nf-dj/cellpilot/client/cellpilot.c

/*
 * Copyright (c) 2015 Netforce Co. Ltd.
 * 
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
 * THE SOFTWARE IS PROVIDED "AS IS", WITHOUT WARRANTY OF ANY KIND,
 * EXPRESS OR IMPLIED, INCLUDING BUT NOT LIMITED TO THE WARRANTIES OF
 * MERCHANTABILITY, FITNESS FOR A PARTICULAR PURPOSE AND NONINFRINGEMENT.
 * IN NO EVENT SHALL THE AUTHORS OR COPYRIGHT HOLDERS BE LIABLE FOR ANY CLAIM,
 * DAMAGES OR OTHER LIABILITY, WHETHER IN AN ACTION OF CONTRACT, TORT OR
 * OTHERWISE, ARISING FROM, OUT OF OR IN CONNECTION WITH THE SOFTWARE OR THE USE
 * OR OTHER DEALINGS IN THE SOFTWARE.
 */

#include <SDL2/SDL.h>
#include <SDL2/SDL_ttf.h>
#include <SDL2/SDL2_gfxPrimitives.h>
#include <lua5.1/lua.h>
#include <lua5.1/lauxlib.h>
#include <lua5.1/lualib.h>
#include <stdlib.h>
#include <string.h>
#include "libavcodec/avcodec.h"
#include <libswscale/swscale.h>
#include <math.h>

lua_State *L;

char screen_text[1024];
uint8_t *picture_data;
int picture_w, picture_h;

AVCodec *codec;
AVCodecContext *codec_ctx;
AVFrame *picture;
int got_frame=0;

SDL_Window *window;
SDL_Renderer *renderer;
SDL_Texture *yuv;
TTF_Font *font;

int ins_bat_volt;

double orig_alt=0;

int prev_timer_t=0;

void on_timer() {
    int res;
    lua_getglobal(L,"on_timer");
    res=lua_pcall(L,0,0,0);
    if (res!=0) {
        error(L,"lua error: %s",lua_tostring(L,-1));
    }
}

void on_key(unsigned char key, int x, int y) {
    int res;
    lua_getglobal(L,"on_key");
    lua_pushlstring(L,&key,1);
    lua_pushnumber(L,x);
    lua_pushnumber(L,y);
    res=lua_pcall(L,3,0,0);
    if (res!=0) {
        error(L,"lua error: %s",lua_tostring(L,-1));
    }
}

int joy_x1=0, joy_y1=0, joy_x2=0, joy_y2=0; 
int JOY_MIN_INTERVAL=100;
int JOY_MAX_INTERVAL=1000;
int prev_joy_axis_change_t=0;
int joy_axis_changed=0;

void on_joy_axis() {
    int res;
    lua_getglobal(L,"on_joy_axis");
    lua_pushnumber(L,joy_x1);
    lua_pushnumber(L,joy_y1);
    lua_pushnumber(L,joy_x2);
    lua_pushnumber(L,joy_y2);
    res=lua_pcall(L,4,0,0);
    if (res!=0) {
        error(L,"lua error: %s",lua_tostring(L,-1));
    }
}

void on_joy_button(int button) {
    int res;
    lua_getglobal(L,"on_joy_button");
    lua_pushnumber(L,button);
    res=lua_pcall(L,1,0,0);
    if (res!=0) {
        error(L,"lua error: %s",lua_tostring(L,-1));
    }
}

void on_joy_hat(int button) {
    int res;
    lua_getglobal(L,"on_joy_hat");
    lua_pushnumber(L,button);
    res=lua_pcall(L,1,0,0);
    if (res!=0) {
        error(L,"lua error: %s",lua_tostring(L,-1));
    }
}

void render_screen() {
    renderer=SDL_CreateRenderer(window,-1,0);
    if (!renderer) {
        printf("failed to create renderer\n");
        exit(1);
    }
    if (got_frame) { // XXX
        SDL_SetRenderDrawColor(renderer,0,0,0,255);
        SDL_RenderFillRect(renderer,NULL);
    }

    SDL_RenderSetLogicalSize(renderer,640,480);

    if (got_frame) {
        yuv=SDL_CreateTexture(renderer,SDL_PIXELFORMAT_YV12,SDL_TEXTUREACCESS_STATIC,320,240);
        if (!yuv) {
            printf("failed to create texture\n");
            exit(1);
        }
        SDL_UpdateYUVTexture(yuv,NULL,picture->data[0],picture->linesize[0],picture->data[1],picture->linesize[1],picture->data[2],picture->linesize[2]);
        SDL_RenderCopy(renderer,yuv,NULL,NULL);
        SDL_DestroyTexture(yuv);
    }

    SDL_Color fg_color={0,255,0};
    SDL_Surface *font_surface=TTF_RenderText_Blended(font,screen_text,fg_color);
    SDL_Texture *font_texture=SDL_CreateTextureFromSurface(renderer,font_surface);
    int font_w, font_h; 
    SDL_QueryTexture(font_texture,NULL,NULL,&font_w,&font_h);
    SDL_Rect font_rect={10,480-font_h-10,font_w,font_h};
    SDL_RenderCopy(renderer,font_texture,NULL,&font_rect);
    SDL_DestroyTexture(font_texture);
    SDL_FreeSurface(font_surface);

    char msg[256];
    sprintf(msg,"V=%.2f",ins_bat_volt/100.0);
    font_surface=TTF_RenderText_Blended(font,msg,fg_color);
    font_texture=SDL_CreateTextureFromSurface(renderer,font_surface);
    SDL_QueryTexture(font_texture,NULL,NULL,&font_w,&font_h);
    SDL_Rect font_rect2={530,480-font_h-10,font_w,font_h};
    SDL_RenderCopy(renderer,font_texture,NULL,&font_rect2);
    SDL_DestroyTexture(font_texture);
    SDL_FreeSurface(font_surface);

    SDL_RenderPresent(renderer);

    SDL_DestroyRenderer(renderer);
}

int decode_video_packet(lua_State *L) {
    AVPacket pkt;
    int got_picture;
    int len;
    //printf("decode_video_packet\n");
    av_init_packet(&pkt);
    pkt.data=(uint8_t*)lua_tolstring(L,1,(size_t*)&pkt.size);
    while (pkt.size>0) {
        len=avcodec_decode_video2(codec_ctx,picture,&got_picture,&pkt);
        //printf("len=%d\n",len);
        if (len<0) {
            printf("Error decoding video frame!\n");
            break;
        }
        if (got_picture) {
            //printf("rendering frame %dx%d\n",picture->width,picture->height);
            got_frame=1;
        } else {
            got_frame=0;
        }
        pkt.size-=len;
        pkt.data+=len;
    }
    return 0;
}

int draw_text(lua_State *L) {
    size_t size;
    uint8_t *buf;
    buf=(uint8_t*)lua_tolstring(L,1,&size);
    strncpy(screen_text,buf,size);
    screen_text[size]=0;
    printf("draw_text '%s'\n",screen_text);
    render_screen();
    return 0;
}

int update_instruments(lua_State *L) {
    size_t size;
    uint8_t *buf;
    ins_bat_volt=(double)lua_tointeger(L,1);
    return 0;
}

int lua_render_screen(lua_State *L) {
    render_screen();
    return 0;
}

void init_video_decode() {
    int res;
    avcodec_register_all();
    codec=avcodec_find_decoder(CODEC_ID_H264);
    if (!codec) {
        printf("video codec not found!\n");
        exit(1);
    }
    codec_ctx=avcodec_alloc_context3(codec);
    codec_ctx->flags|=CODEC_FLAG_LOW_DELAY;
    codec_ctx->flags2|=CODEC_FLAG2_CHUNKS;
    res=avcodec_open2(codec_ctx,codec,NULL);
    picture=avcodec_alloc_frame();
    if (res<0) {
        printf("failed to open codec!\n");
        exit(1);
    }
}

void set_drone_address(char *host, int port) {
    int res;
    lua_getglobal(L,"set_drone_address");
    lua_pushlstring(L,host,strlen(host));
    lua_pushnumber(L,port);
    res=lua_pcall(L,2,0,0);
    if (res!=0) {
        error(L,"lua error: %s",lua_tostring(L,-1));
    }
}

int main(int argc, char **argv) {
    int res;
    float display_w;
    float border;
    SDL_Joystick *joy;
    SDL_Event event;

    res=SDL_Init(SDL_INIT_VIDEO|SDL_INIT_JOYSTICK);
    if (res<0) {
        printf("failed to init SDL\n");
        exit(1);
    }
    res=SDL_NumJoysticks();
    printf("num_joysticks=%d\n",res);
    if (res<=0) {
        printf("joystick not found\n");
        exit(1);
    }

    SDL_JoystickEventState(SDL_ENABLE);
    joy=SDL_JoystickOpen(0);

    window=SDL_CreateWindow("Cellpilot",SDL_WINDOWPOS_UNDEFINED,SDL_WINDOWPOS_UNDEFINED,640,480,SDL_WINDOW_SHOWN|SDL_WINDOW_RESIZABLE);
   // window=SDL_CreateWindow("Cellpilot",SDL_WINDOWPOS_UNDEFINED,SDL_WINDOWPOS_UNDEFINED,0,0,SDL_WINDOW_FULLSCREEN_DESKTOP);
    if (!window) {
        printf("failed to create window\n");
        exit(1);
    }

    TTF_Init();
    font = TTF_OpenFont("DroidSans.ttf", 25);
    if (!font) {
        printf("failed to open font\n");
        exit(1);
    }

    init_video_decode();

    L=luaL_newstate();
    luaL_openlibs(L);
    lua_register(L,"draw_text",draw_text);
    lua_register(L,"update_instruments",update_instruments);
    lua_register(L,"decode_video_packet",decode_video_packet);
    lua_register(L,"render_screen",lua_render_screen);

    res=luaL_dofile(L,"cellpilot.lua");
    if (res!=0) {
        error(L,"lua error: %s",lua_tostring(L,-1));
        return -1;
    }

    if (argc<3) {
        printf("Usage: cellpilot DRONE_HOST DRONE_PORT\n");
        return -1;
    }
    char *drone_host=argv[1];
    int drone_port=atoi(argv[2]);
    set_drone_address(drone_host,drone_port);

    while (1) {
        int t;
        const char *key_name;
        res=SDL_WaitEventTimeout(&event,10);
        t=SDL_GetTicks();
        SDL_StartTextInput();
        if (res) {
            switch (event.type) {
                case SDL_KEYDOWN:
                    key_name=SDL_GetKeyName(event.key.keysym.sym);
                    printf("key down %d %s\n",event.key.keysym.scancode,key_name);
                    int code=event.key.keysym.scancode;
                    if (code==79) {
                        on_key('l',0,0);
                    } else if (code==80) {
                        on_key('h',0,0);
                    } else if (code==81) {
                        on_key('j',0,0);
                    } else if (code==82) {
                        on_key('k',0,0);
                    }
                    break;
                case SDL_TEXTINPUT:
                    printf("#################################################################\n");
                    printf("text: %s\n",event.text.text);
                    on_key(event.text.text[0],0,0);
                    break;
                case SDL_JOYAXISMOTION:
                    //printf("joy axis %d %d\n",event.jaxis.axis,event.jaxis.value);
                    if (event.jaxis.axis==0) {
                        joy_x1=event.jaxis.value;
                    } else if (event.jaxis.axis==1) {
                        joy_y1=-event.jaxis.value;
                    } else if (event.jaxis.axis==3) {
                        joy_x2=event.jaxis.value;
                    } else if (event.jaxis.axis==4) {
                        joy_y2=-event.jaxis.value;
                    }
                    joy_axis_changed=1;
                    break;
                case SDL_JOYBUTTONDOWN:
                    //printf("joy button %d\n",event.jbutton.button);
                    on_joy_button(event.jbutton.button);
                    break;
                case SDL_JOYHATMOTION:
                    //printf("joy hat %d\n",event.jhat.value);
                    on_joy_hat(event.jhat.value);
                    break;
                case SDL_QUIT:
                    printf("quit");
                    exit(0);
                    break;
            }
        }
        if (!prev_joy_axis_change_t || t-prev_joy_axis_change_t>=JOY_MAX_INTERVAL) {
            on_joy_axis();
            prev_joy_axis_change_t=t;
            joy_axis_changed=0;
        } else if (joy_axis_changed) {
            if (!prev_joy_axis_change_t || t-prev_joy_axis_change_t>=JOY_MIN_INTERVAL) {
                on_joy_axis();
                prev_joy_axis_change_t=t;
                joy_axis_changed=0;
            }
        }
        if (!prev_timer_t || t-prev_timer_t>=10) {
            on_timer();
            prev_timer_t=t;
        }
    }

    return 0;
}
